SouravB97/Cansat-2019-Team-BAGS-Electronics/Electronics/Arduino Code/cansat_sectionA/packet.h

/*
 * packet.h
 */
#include<Arduino.h>
#ifndef packet_h
#define packet_h

enum op_state {
	boot,							//state when packet initialised 
	idle, 						//cansat is transmitting telemetry on the launch pad
	launch_detect, 		//cansat is launched in the rocket and in the air
	deploy,						//cansat has seperated from the rocket
	payload_release,	//payload has seperated from the container
	landed,						//payload has landed to the ground and is awaiting recovery.
};
const String op_state_string_lut[] = {
	"Boot", "Idle", "Launch detect", "Deploy", "Payload Released", "Landed"
};

class packet {
  public:
		packet(const uint16_t team_id = 1516);	//assigned to BAGS
		
		/*
		Variables to be transmitted
		Minimum Total Size = 50 bytes
		*/
		
		uint16_t team_id;			// the assigned team identification
		volatile uint16_t mission_time;	//the time since initial power up in seconds
		volatile uint16_t packet_count;	// the count of transmitted packets, which is to be maintained through processor reset.
		volatile float altitude;	// the altitude in units of meters and must be relative to ground level. The resolution must be 0.1 meters.
		volatile float pressure;	//the measurement of atmospheric pressure in units of pascals. The resolution must be 0.1 pascals.
		volatile float temperature;	// the sensed temperature in degrees C with one tenth of a degree resolution.
		volatile float voltage;		//the voltage of the CanSat power bus. The resolution must be 0.01 volts.
		String gps_time;		// the time generated by the GPS receiver. The time must be reported in UTC and have a resolution of a second. UTC Format: 2013-10-22T01:37:56+05:30
		volatile float gps_lattitude;	//the latitude generated by the GPS receiver in decimal degrees with a resolution of 0.0001 degrees.
		volatile float gps_longitude;	//the longitude generated by the GPS receiver in decimal degrees with a resolution of 0.0001 degrees.
		volatile float gps_altitude;	//the altitude generated by the GPS receiver in meters above mean sea level with a resolution of 0.1 meters.
		volatile uint8_t gps_sats;		// the number of GPS satellites being tracked by the GPS receiver. This must be an integer number.
		volatile float pitch;			// the tilt angle in the pitch axis in degrees. The resolution must be 1 degree.
		volatile float roll;			// the tilt angle of the roll axis in degrees. The resolution must be 1 degree.
		volatile int blade_spin_rate;	// the rate the auto-gyro blades spin relative to the science payload. The units must be in revolutions per minute (rpm). The resolution must be 1 rpm.
		volatile op_state software_state;			// the operating state of the software. (boot, idle, launch detect, deploy, etc.)
		volatile int bonus_direction;	// the direction the camera is pointed relative to earth’s magnetic north specified in degrees.
		
		//Other variables
		String _csv_string;			//locally stores output of toString()
		//volatile uint32_t gps_time;
		const String format = "team_id, time, count, altitude, pressure, temperature, voltage, gps time, lattitude, longitude, gps altitude, satellites, pitch, role, spin rate, softwar state, direction";
		
		String toString();			//returns a csv string of all the data fields.
    void display();         //prints the packet to the terminal
	
};

#endif // packet_h
